k-antoniou/FelineWatchdog/Images/3dCaseClosed.png

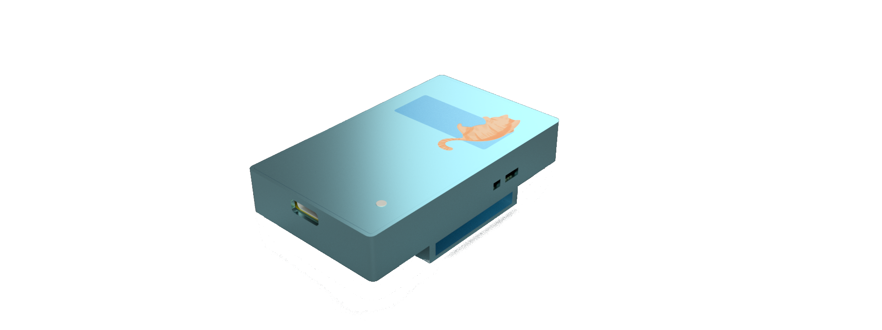
Images/3dCaseClosed.png
